codepainters/FD1/firmware/src/keyboard.c

/**
 * Copyright (c) 2014, Przemyslaw Wegrzyn <pwegrzyn@codepainters.com>
 * All rights reserved.
 *
 * This file is distributed under the Modified BSD License.
 * See LICENSE.txt for details.
 */

#include "sysdefs.h"

#include "keyboard.h"
#include "keyboard_defs.h"
#include "settings.h"
#include "midi.h"

// per-key state
typedef struct {
    // debounce counter is initailized with DEBOUNCE_PERIOD and counts down
    int debounceCounter;
    // previous-tick state of the key (without debouncing)
    int previousState;
    // true, if key is considered pressed at the moment
    bool pressed;

    // if true, NOTE ON message was sent, and NOTE OFF shall be enqueued
    // once the key is released
    bool noteOnSent;

    // MIDI note params for the pressed key
    unsigned int midiNote;
    unsigned int midiVelocity;
    unsigned int midiChannel;
} KeyState_t;

// key states
static KeyState_t keys[KBD_TOTAL_KEYS];

// current scan row of the matrix keyboard
static unsigned int currentScanRow = 0;

static void Keyboard_HandleKeyAction(const unsigned int index);

void Keyboard_Init()
{
    for (unsigned int i = 0; i < KBD_TOTAL_KEYS; i++) {
        keys[i].debounceCounter = 0;
        keys[i].previousState = 0;
        keys[i].pressed = false;
        keys[i].noteOnSent = false;
    }

    for (unsigned int i = 0; i < KBD_ROWS; i++) {
        GpioPin_ConfigureOut(&KBD_ROW_PINS[i], 1);
    }

    for (unsigned int i = 0; i < KBD_COLUMNS; i++) {
        GpioPin_ConfigureIn(&KBD_COLUMN_PINS[i]);
    }

    GpioPin_SetState(&KBD_ROW_PINS[currentScanRow], 0);
}

void Keyboard_TimerTick()
{
    // Note: column lines needs some time to charge/discharge, thus we can't read it back immediately after
    // switching the row. On each cycle we read the row preselected on the previous cycle, thus giving a whole
    // cycle time for the values to settle.

    for (unsigned int column = 0; column < KBD_COLUMNS; column++) {
        unsigned int state = GpioPin_GetState(&KBD_COLUMN_PINS[column]) ^ 0x01;

        unsigned int index = KBD_KEY_INDEX(currentScanRow, column);
        KeyState_t* key = &keys[index];

        if (!key->pressed) {
            // for press detection we accept first rising edge (i.e. no debouncing) to make attack timing better
            if (key->previousState == 0 && state == 1) {
                key->pressed = true;
                Keyboard_HandleKeyAction(index);
            }
        }
        else {
            // for key release detection regular debouncing is performed
            if (state == 0) {
                if (key->previousState == 1) {
                    key->debounceCounter = DEBOUNCE_PERIOD;
                }
                else if(--key->debounceCounter == 0) {
                    key->pressed = false;
                    Keyboard_HandleKeyAction(index);
                }
            }
        }

        key->previousState = state;
    }

    // Disable current row and advance to next one
    GpioPin_SetState(&KBD_ROW_PINS[currentScanRow], 1);
    currentScanRow = (currentScanRow + 1) % KBD_ROWS;
    GpioPin_SetState(&KBD_ROW_PINS[currentScanRow], 0);
}

static void Keyboard_HandleKeyAction(const unsigned int index)
{
    KeyState_t* key = &keys[index];

    if(key->pressed) {
        int note = KBD_LEFTMOST_NOTE + (settings.octave * 12) + index;
        // ensure key is not "active" (i.e. no pending NOTE OFF)
        if (note >= 0 && !key->noteOnSent) {
            // set note parameters
            key->midiChannel = settings.midiChannel;
            key->midiVelocity = settings.velocity;
            key->midiNote = note;
            key->noteOnSent = MIDI_QueueNoteOn(key->midiChannel, key->midiNote, key->midiVelocity);
        }
    }
    else if (key->noteOnSent) {
        // NOTE ON was previously sent and key was just depressed -> send NOTE OFF
        MIDI_QueueNoteOff(key->midiChannel, key->midiNote, key->midiVelocity);
        key->noteOnSent = false;
    }
}
